timschmidt/parameterized-mendel/v1.0/y-bearing-180-inner_2off.stl

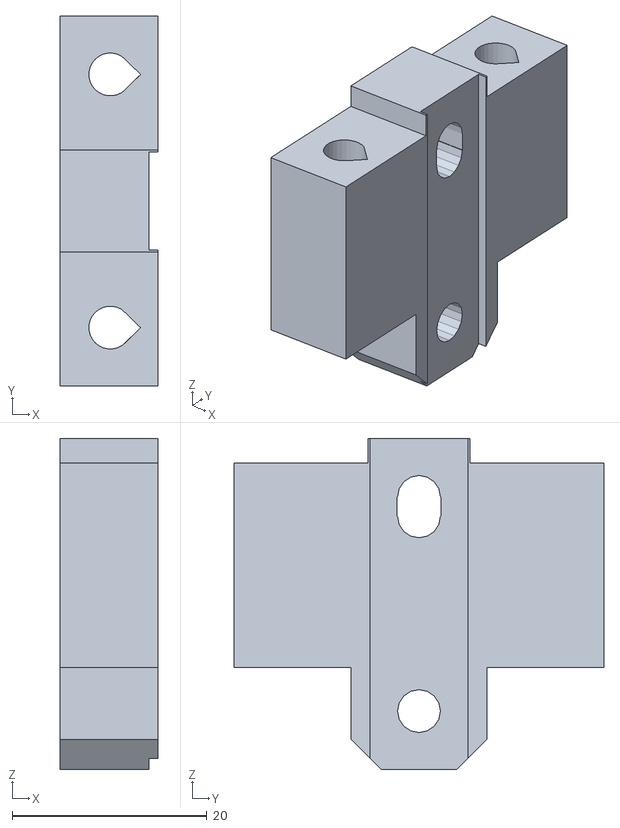
[picture p15: CAD file, 2010-05-11, an earlier design]
v1.0/y-bearing-180-inner_2off.stl
10.1 x 38.0 x 34.0
