timschmidt/parameterized-mendel/v1.0/x-axis-side-plate-nut-jig_2off.stl

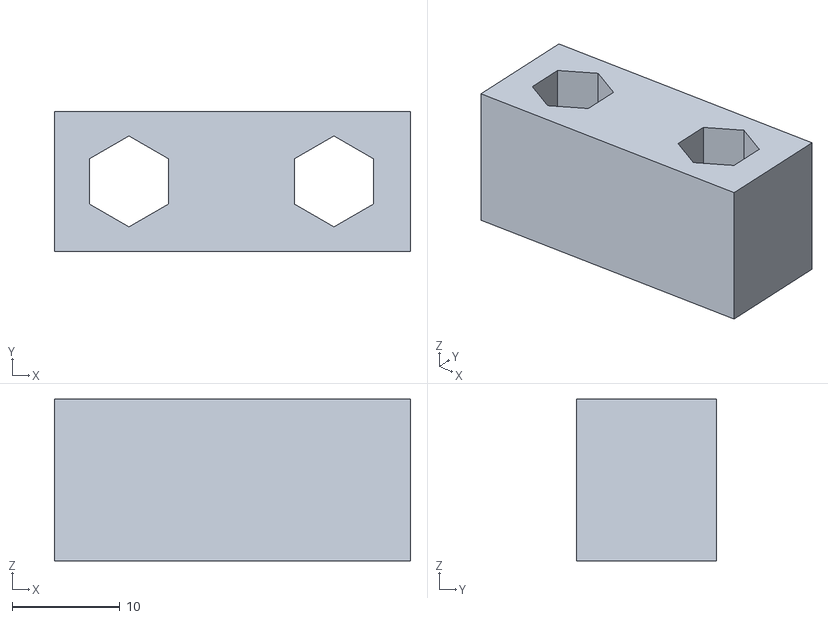
[picture p16: CAD file, 2010-05-11, an earlier design]
v1.0/x-axis-side-plate-nut-jig_2off.stl
33.0 x 13.0 x 15.0
